Bogdan594/InkTime-Smartwatch/Images/Baterie3D.png

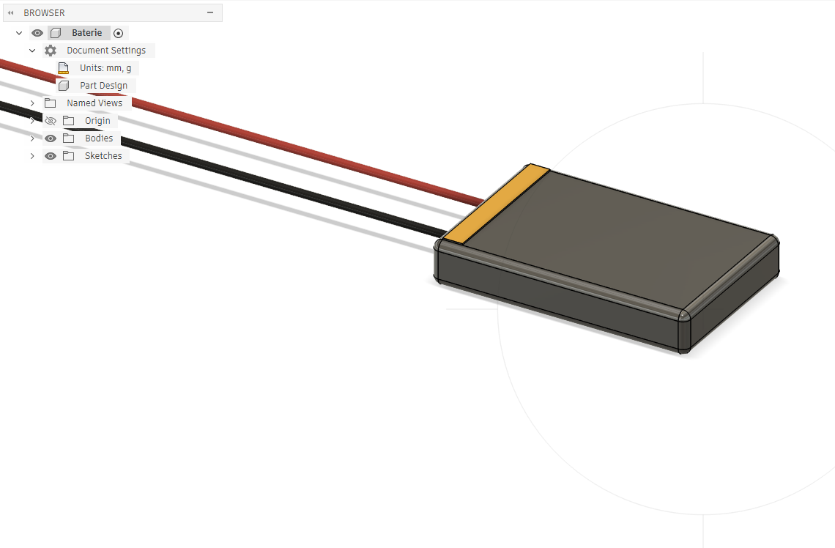
Images/Baterie3D.png
