Bogdan594/InkTime-Smartwatch/Images/Model3D_2.png

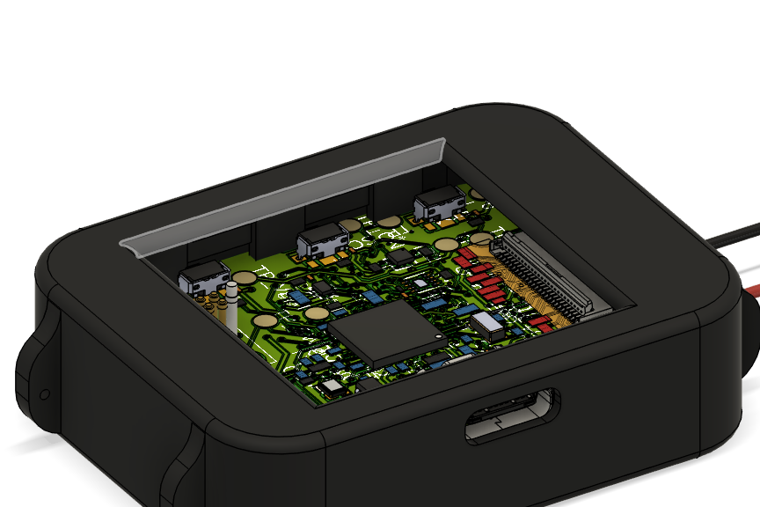
Images/Model3D_2.png
