Bogdan594/InkTime-Smartwatch/Images/PCB_3D_BOTTOM.png

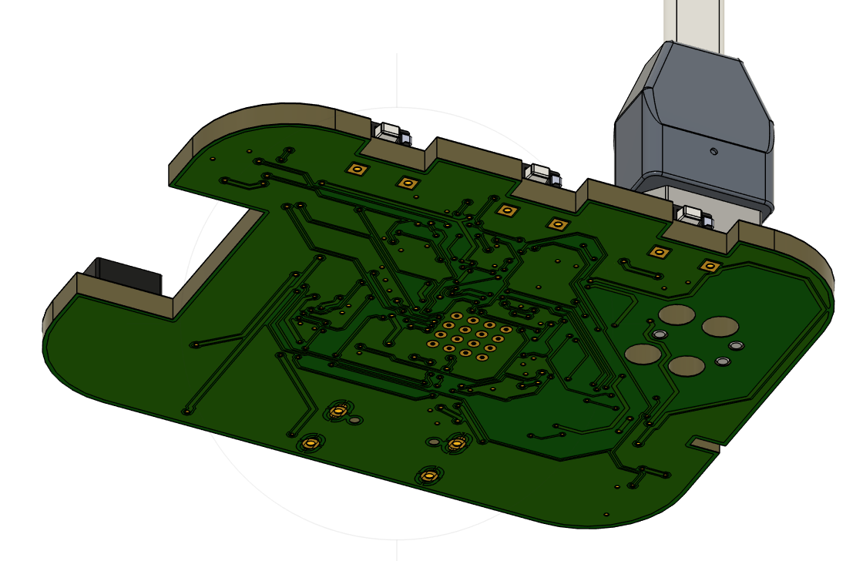
Images/PCB_3D_BOTTOM.png
